Tinkerforge/led-strip-v2-bricklet/software/src/ws281x_lut.c

/* led-strip-v2-bricklet
 * Copyright (C) 2018 Olaf Lüke <olaf@tinkerforge.com>
 *
 * ws281x_lut.c: Lookup table for WS2811 and WS2812 bits
 *
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
 * You should have received a copy of the GNU Lesser General Public
 * License along with this library; if not, write to the
 * Free Software Foundation, Inc., 59 Temple Place - Suite 330,
 * Boston, MA 02111-1307, USA.
 */

#include <stdint.h>

const uint32_t ws281x_lut[256] = {
	0b1110111011101110111011101110111, 
	0b1110111011101110111011101110001, 
	0b1110111011101110111011100010111, 
	0b1110111011101110111011100010001, 
	0b1110111011101110111000101110111, 
	0b1110111011101110111000101110001, 
	0b1110111011101110111000100010111, 
	0b1110111011101110111000100010001, 
	0b1110111011101110001011101110111, 
	0b1110111011101110001011101110001, 
	0b1110111011101110001011100010111, 
	0b1110111011101110001011100010001, 
	0b1110111011101110001000101110111, 
	0b1110111011101110001000101110001, 
	0b1110111011101110001000100010111, 
	0b1110111011101110001000100010001, 
	0b1110111011100010111011101110111, 
	0b1110111011100010111011101110001, 
	0b1110111011100010111011100010111, 
	0b1110111011100010111011100010001, 
	0b1110111011100010111000101110111, 
	0b1110111011100010111000101110001, 
	0b1110111011100010111000100010111, 
	0b1110111011100010111000100010001, 
	0b1110111011100010001011101110111, 
	0b1110111011100010001011101110001, 
	0b1110111011100010001011100010111, 
	0b1110111011100010001011100010001, 
	0b1110111011100010001000101110111, 
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
	0b1110111011101110111000101110111,
	0b10111011101110111000101110111,
	0b1110001011101110111000101110111,
	0b10001011101110111000101110111,
	0b1110111000101110111000101110111,
	0b10111000101110111000101110111,
	0b1110001000101110111000101110111,
	0b10001000101110111000101110111,
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
};

#endif
